jakspacek/GCC-Backmounts/Pictures/IMG_3669.jpg

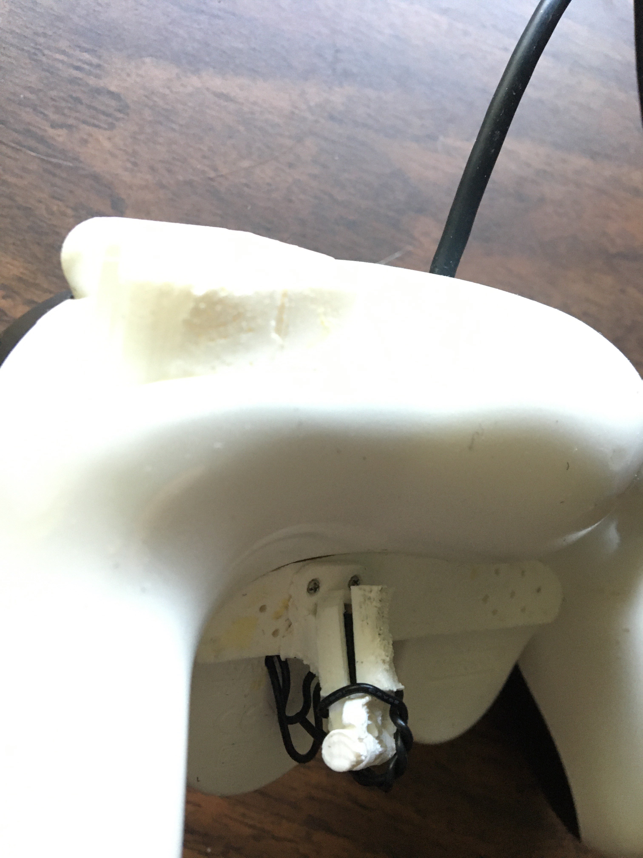
Pictures/IMG_3669.jpg
