jakspacek/GCC-Backmounts/Pictures/IMG_3670.jpg

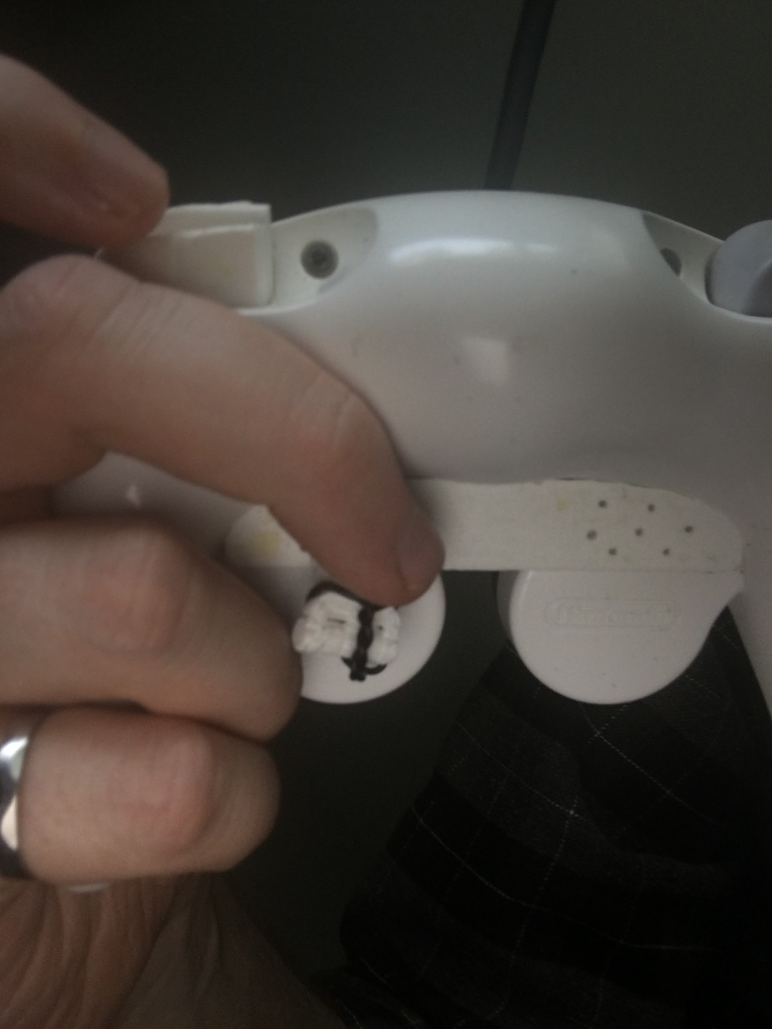
Pictures/IMG_3670.jpg
